kanstantsin-bucha/dg-manufacturing-docs/housing/enclosure/DAir-Lily/Models/Model of Top PCB/Upper_pcb_with_lcds_buttons_bme_CIRCULAR.SLDASM

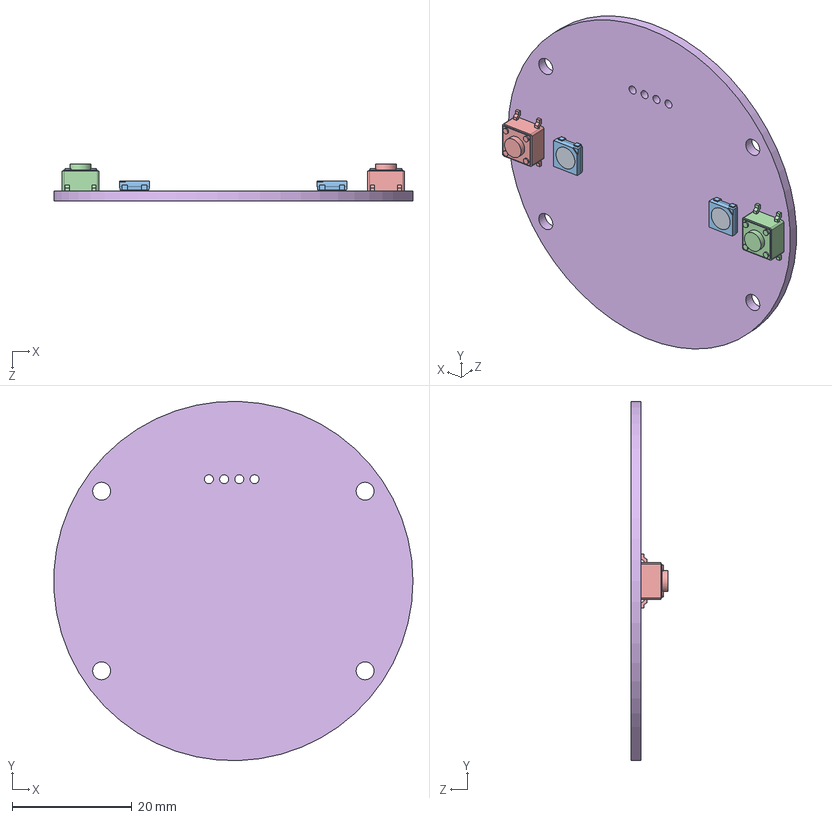
[picture p20: CAD file, 2020-05-26]
housing/enclosure/DAir-Lily/Models/Model of Top PCB/Upper_pcb_with_lcds_buttons_bme_CIRCULAR.SLDASM
59.9 x 60.0 x 6.19 mm
User Library-WS2812B x 2
User Library-WS2812B-1 x 2
User Library-WS2812B-2 x 2
Board-Part-1-1
