kanstantsin-bucha/dg-manufacturing-docs/housing/enclosure/DAir-Lily/Models/Model of Bottom PCB/bottom_test_pcb.SLDASM

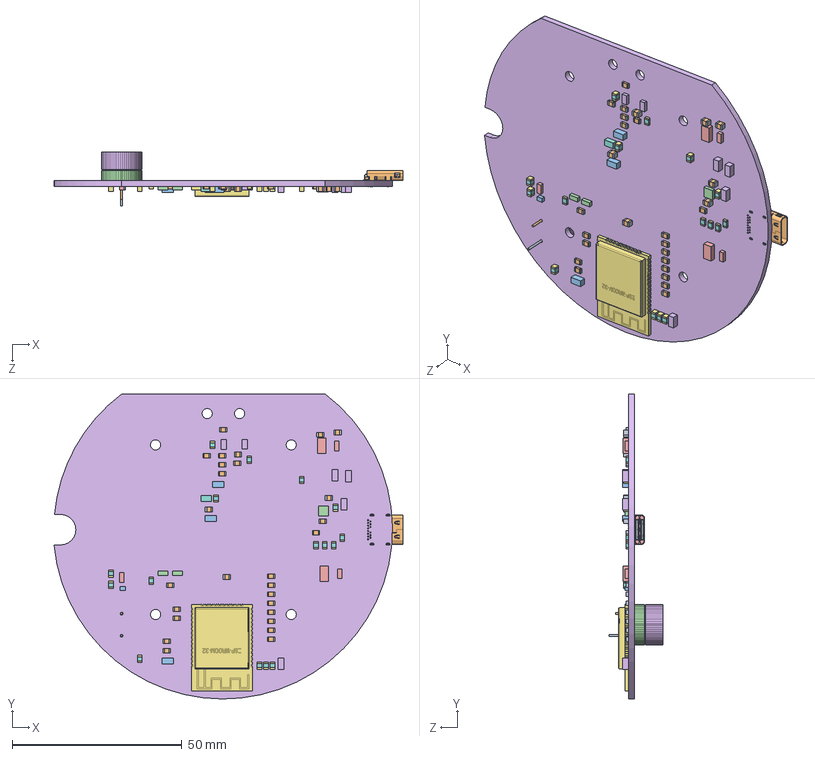
[picture p21: CAD file, 2020-05-26]
housing/enclosure/DAir-Lily/Models/Model of Bottom PCB/bottom_test_pcb.SLDASM
102.9 x 89.9 x 16.0 mm
632723300011_Shielding_2 x 2
632723300011_Housing_Bottom3
632723300011_PIN7_Bottom_v3_mir
632723300011_PIN5_Bottom_v3_mir
632723300011_PIN2_Bottom_v3_mir
632723300011_PIN6_Bottom_v3_mir
632723300011_PIN4_Bottom_v3_mir
632723300011_PIN1_Bottom_v3_mir
632723300011_PIN2_Top_v3 x 8
632723300011_PIN7_Bottom_v3
632723300011_PIN6_Bottom_v3
632723300011_PIN5_Bottom_v3
632723300011_PIN4_Bottom_v3
632723300011_PIN2_Bottom_v3
632723300011_PIN1_Top_v3 x 4
632723300011_PIN1_Bottom_v3
632723300011_Housing_Bottom
632723300011_Shielding_1_v3
632723300011_Housing_TOP
632723300011_Shielding_3_v3
632723300011_Housing
Extruded x 4
Extruded-1 x 20
Extruded-2 x 10
Extruded-3 x 14
Extruded-4 x 7
Extruded-5 x 3
Extruded-6
Extruded-7 x 2
Extruded-8 x 2
User Library-esp-wroom-32
Extruded-9
Extruded-10
Extruded-11
Extruded-12
Extruded-13 x 12
Extruded-14 x 6
Extruded-15 x 40
Extruded-16 x 20
Extruded-17
Extruded-18 x 2
Extruded-19 x 3
Board-Part-1
