kanstantsin-bucha/dg-manufacturing-docs/housing/Other Models/Сonverter.SLDASM

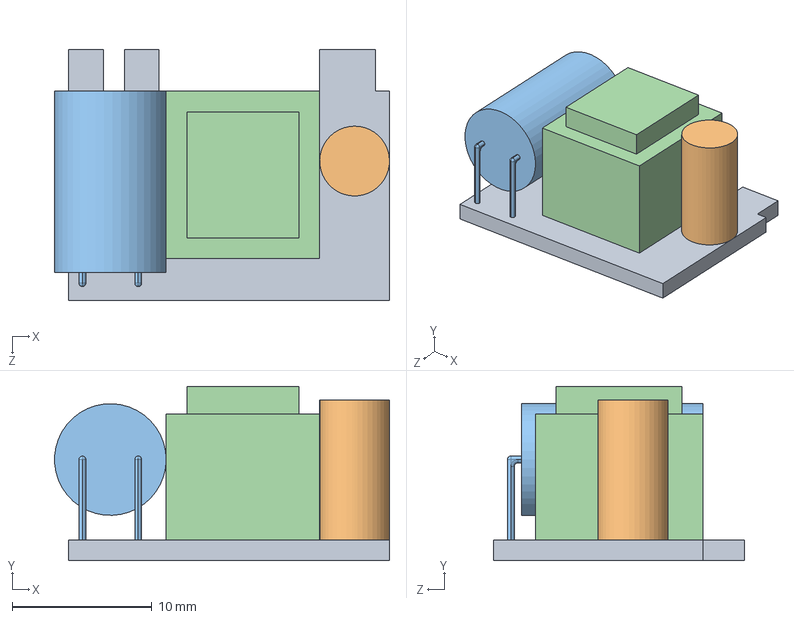
[picture p22: CAD file, 2020-05-26]
housing/Other Models/Сonverter.SLDASM
24.0 x 12.5 x 18.0 mm
Плата
Конденс.верт
Конденс.горизонт.
Трансф
